ikatkov/rf-power-meter-qrp/ltspice/power-ripple-filter.asc

C1: cap; 100µ
C2: cap; 100µ
L1: ind; 250µ
R1: res; 0.1
R2: res; 2
V1: voltage; 5; Rser=1
V3: voltage; PWL REPEAT FOREVER (0 0 10u 0.2 10.01u 0) ENDREPEAT
Named nets: 0, OUT, in
.ac dec 100 1Meg 50Meg
.tran 0 2m 1m
