ikatkov/rf-power-meter-qrp/ltspice/qrt-rf-power-meter-shunt-cap-compensation.asc

C1: cap; 10n
C3: cap; 10n
C-freq-comp: cap; 5p
D1: diode; 1N5711
L1: ind; 40n
R2: res; 50
R4: res; 12.5k
V1: voltage; 10
V2: signal; SINE(0 200 7Meg); AC 1; Rser=50
Named nets: 0, OUT, in
.ac dec 100 1Meg 50Meg
.net I(R1) V2
.MODEL 1N5711 D IS=5.5987n N=1.0023 RS=30.053 IKF=19.036  cjo=1.7605p
+ M=.20029 VJ=.3905 ISR=24.229n NR=4.1695 FC=0.5 TT=0 XTI=2
*$
.tran 10u
50V
DC block
stray
